RetroLoom/LPT2FDD/Images/LPT2FDD_3D.png

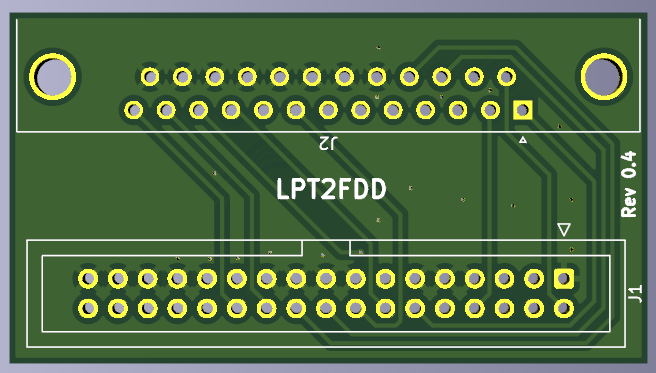
Images/LPT2FDD_3D.png
