RetroLoom/LPT2FDD/Power Adapter - PS2/4x1md/docs/images/3.5mm_6_contacts_4_conductors_audio_plug.png

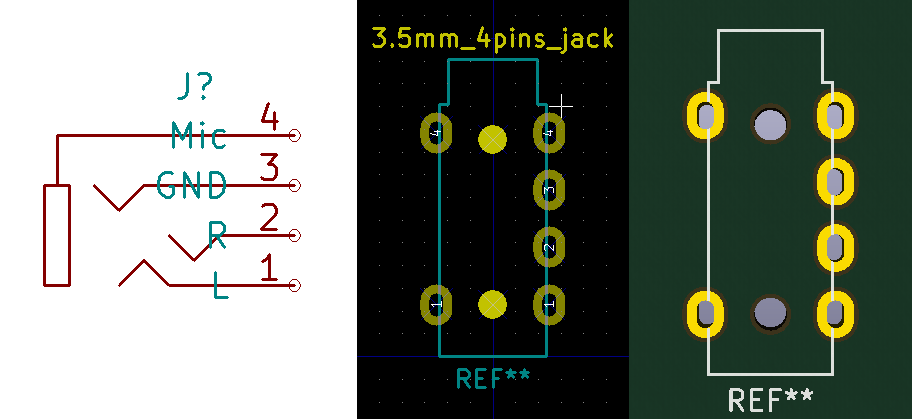
Power Adapter - PS2/4x1md/docs/images/3.5mm_6_contacts_4_conductors_audio_plug.png
