RetroLoom/LPT2FDD/Power Adapter - PS2/4x1md/docs/images/Connector_MiniDIN_Female_6Pin_2rows_footprints.png

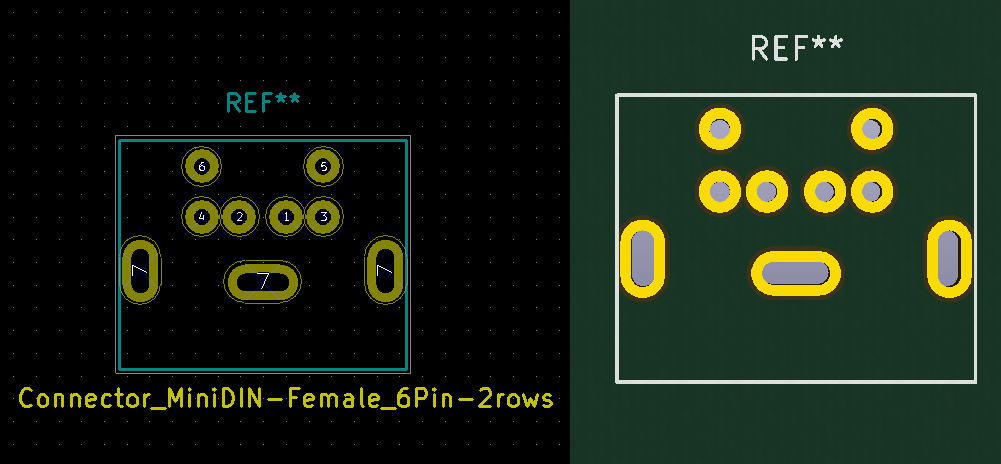
Power Adapter - PS2/4x1md/docs/images/Connector_MiniDIN_Female_6Pin_2rows_footprints.png
