RetroLoom/LPT2FDD/Power Adapter - PS2/4x1md/docs/images/datasheets/Cliff_UT1x.png

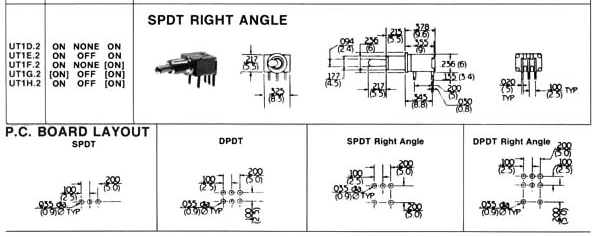
Power Adapter - PS2/4x1md/docs/images/datasheets/Cliff_UT1x.png
