RetroLoom/LPT2FDD/Power Adapter - PS2/4x1md/docs/images/datasheets/Connector_MiniDIN_Female_6Pin_2rows.png

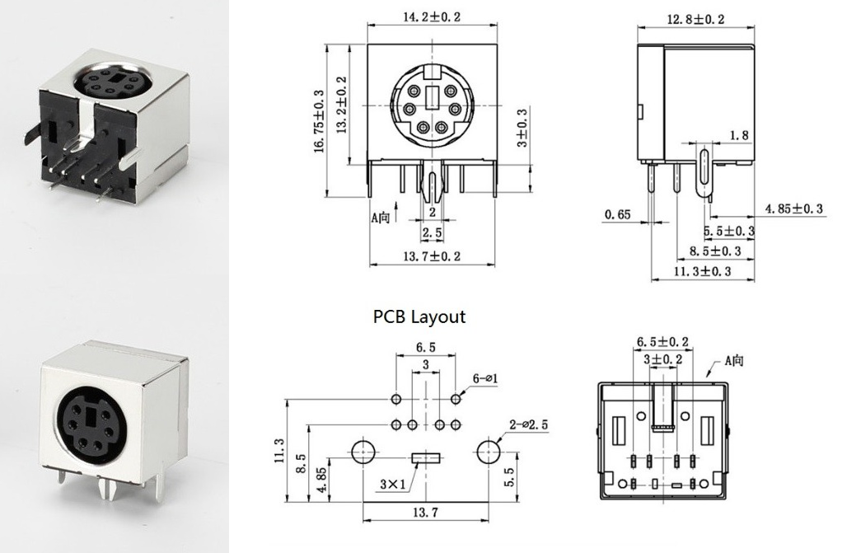
Power Adapter - PS2/4x1md/docs/images/datasheets/Connector_MiniDIN_Female_6Pin_2rows.png
