RetroLoom/LPT2FDD/Power Adapter - PS2/4x1md/docs/images/datasheets/Gms-g9_GNSS_Module.png

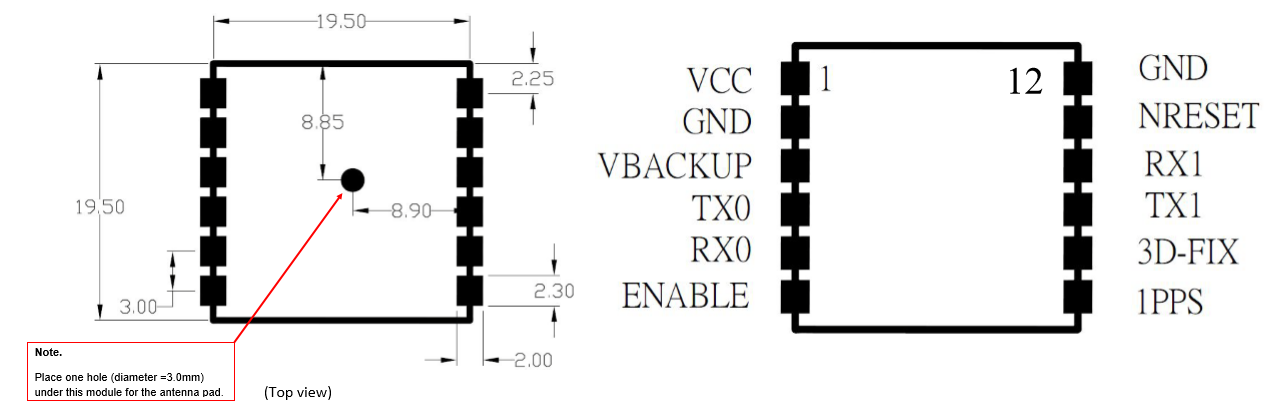
Power Adapter - PS2/4x1md/docs/images/datasheets/Gms-g9_GNSS_Module.png
