RetroLoom/LPT2FDD/Power Adapter - PS2/4x1md/docs/images/datasheets/Jack PJ-311D.jpg

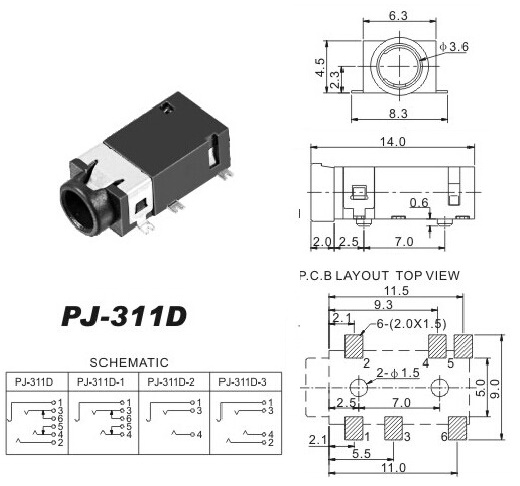
Power Adapter - PS2/4x1md/docs/images/datasheets/Jack PJ-311D.jpg
