RetroLoom/LPT2FDD/Power Adapter - PS2/4x1md/docs/images/datasheets/Philmore_30-20001_SPDT_Switch.png

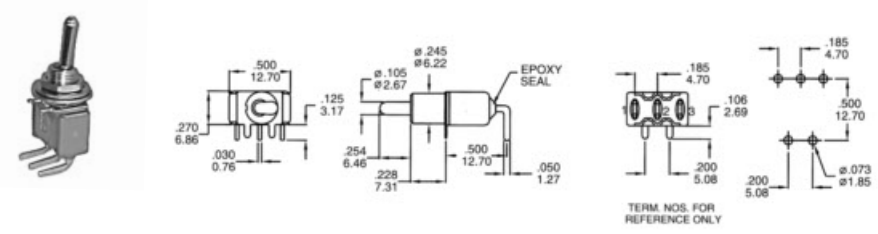
Power Adapter - PS2/4x1md/docs/images/datasheets/Philmore_30-20001_SPDT_Switch.png
