RetroLoom/LPT2FDD/Power Adapter - PS2/4x1md/docs/images/datasheets/PJ-320DS.png

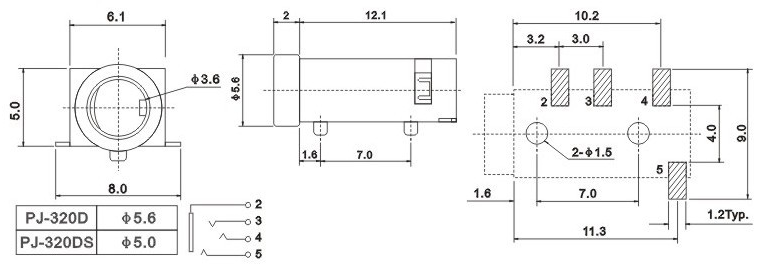
Power Adapter - PS2/4x1md/docs/images/datasheets/PJ-320DS.png
