RetroLoom/LPT2FDD/Power Adapter - PS2/4x1md/docs/images/datasheets/Quectel_L80_GPS_Module_2.png

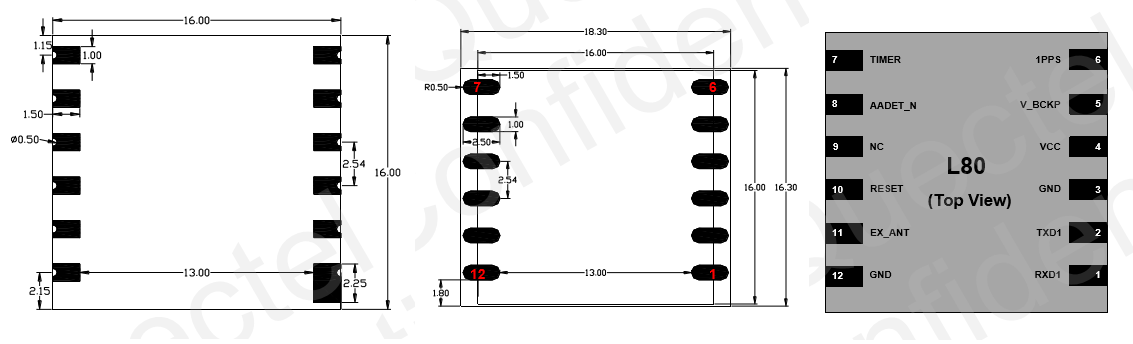
Power Adapter - PS2/4x1md/docs/images/datasheets/Quectel_L80_GPS_Module_2.png
