RetroLoom/LPT2FDD/Power Adapter - PS2/4x1md/docs/images/datasheets/Seiko_MS621FE-FL11E_dia.png

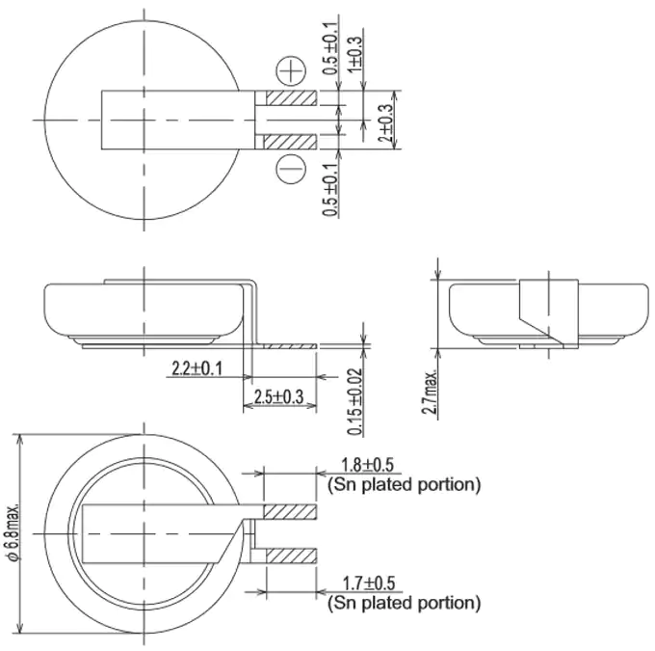
Power Adapter - PS2/4x1md/docs/images/datasheets/Seiko_MS621FE-FL11E_dia.png
