RetroLoom/LPT2FDD/Power Adapter - PS2/4x1md/docs/images/datasheets/USB Micro 5 pin SMT B.jpg

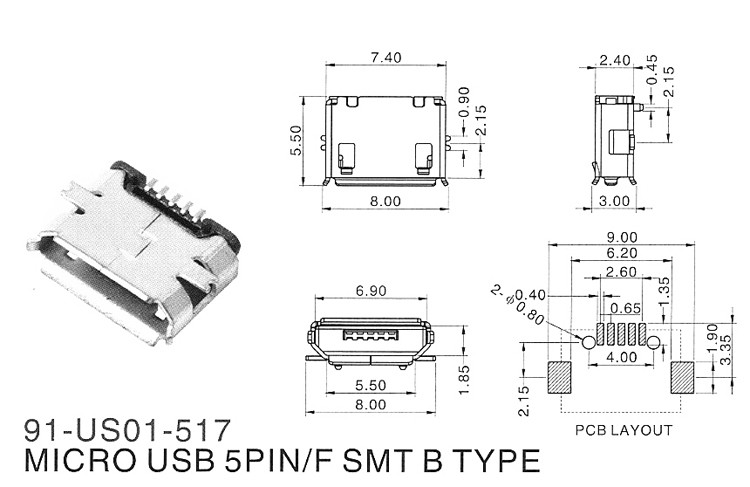
Power Adapter - PS2/4x1md/docs/images/datasheets/USB Micro 5 pin SMT B.jpg
