RetroLoom/LPT2FDD/Power Adapter - PS2/4x1md/docs/images/datasheets/USB Micro 5pin Through hole.jpg

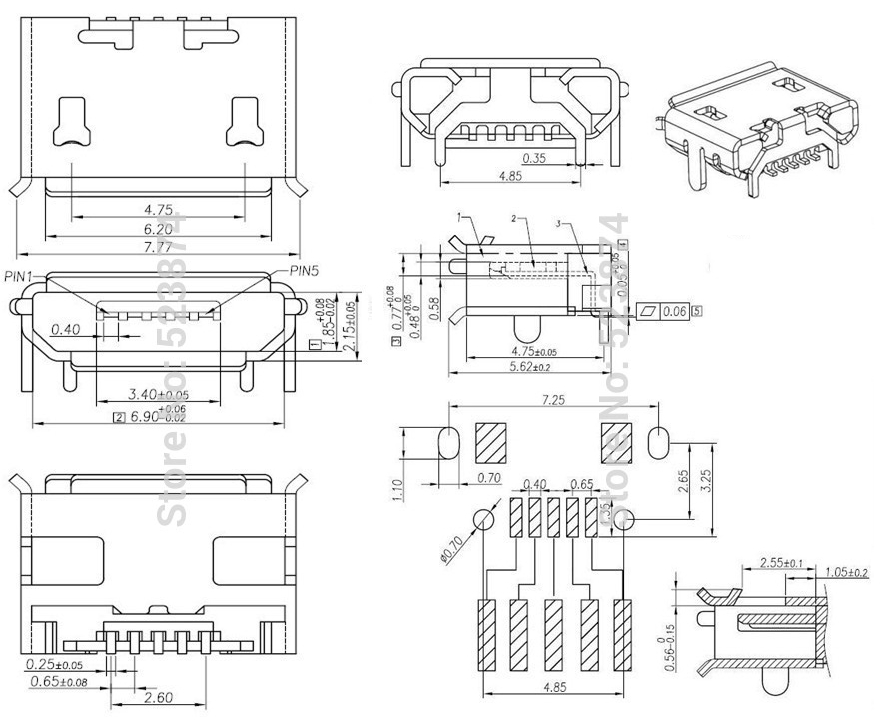
Power Adapter - PS2/4x1md/docs/images/datasheets/USB Micro 5pin Through hole.jpg
