RetroLoom/LPT2FDD/Power Adapter - PS2/4x1md/docs/images/datasheets/USB_Mini_Vertical.jpg

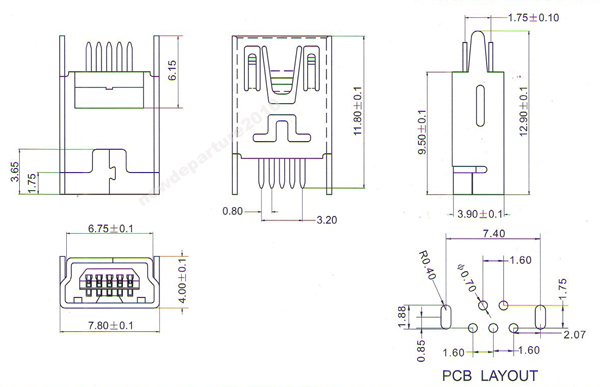
Power Adapter - PS2/4x1md/docs/images/datasheets/USB_Mini_Vertical.jpg
