RetroLoom/LPT2FDD/Power Adapter - PS2/4x1md/docs/images/footprints_01.png

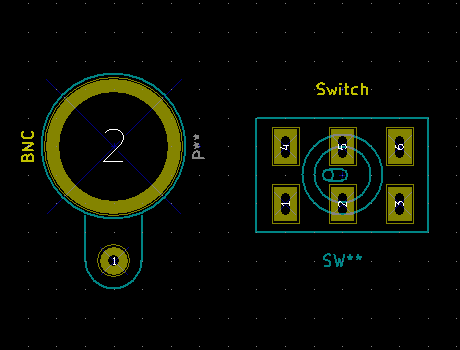
Power Adapter - PS2/4x1md/docs/images/footprints_01.png
