RetroLoom/LPT2FDD/Power Adapter - PS2/4x1md/docs/images/microampermeter.jpg

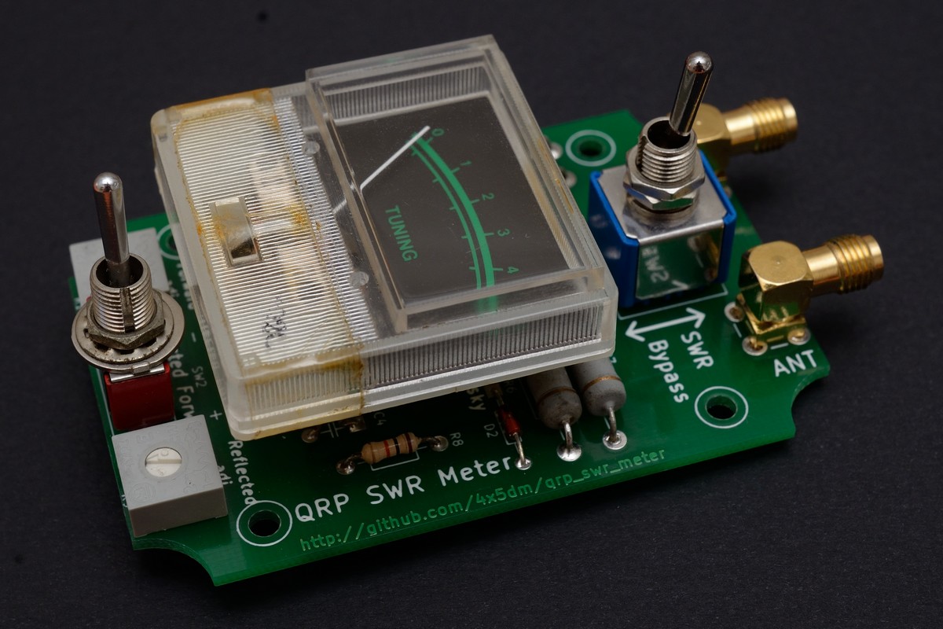
Power Adapter - PS2/4x1md/docs/images/microampermeter.jpg
