RetroLoom/LPT2FDD/Power Adapter - PS2/4x1md/docs/images/microampermeter.png

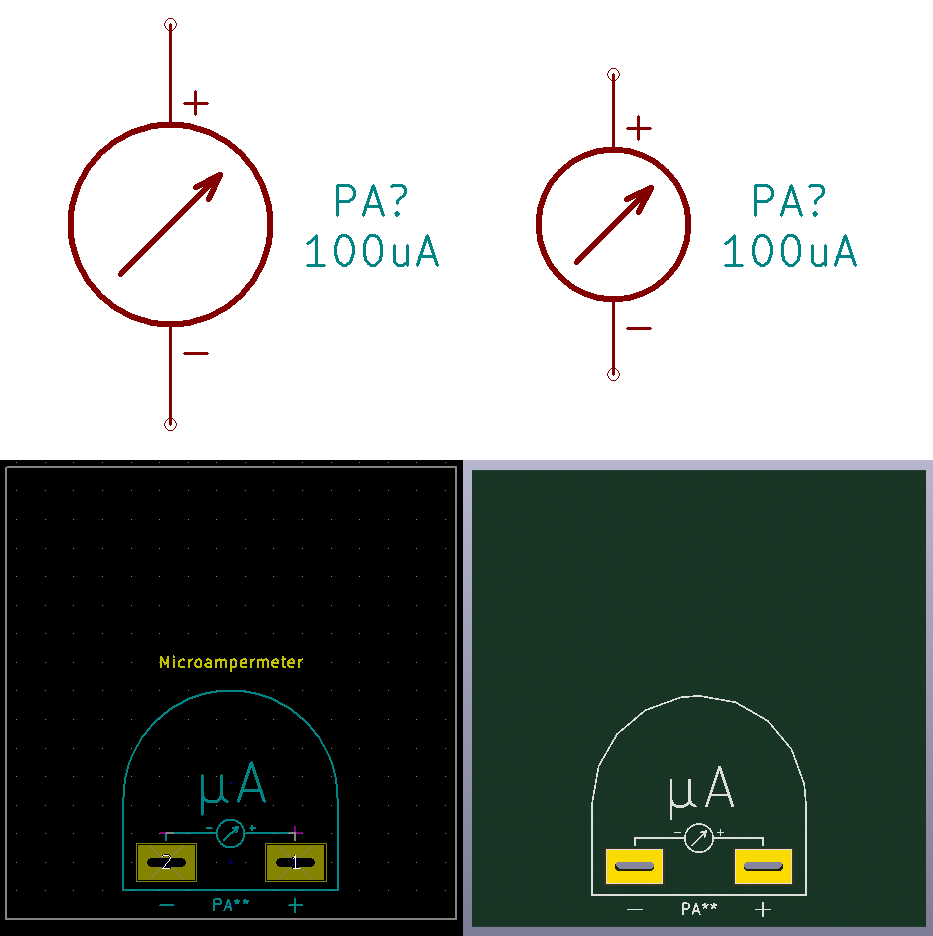
Power Adapter - PS2/4x1md/docs/images/microampermeter.png
