RetroLoom/LPT2FDD/Power Adapter - PS2/4x1md/docs/images/mini_usb_throughhole.png

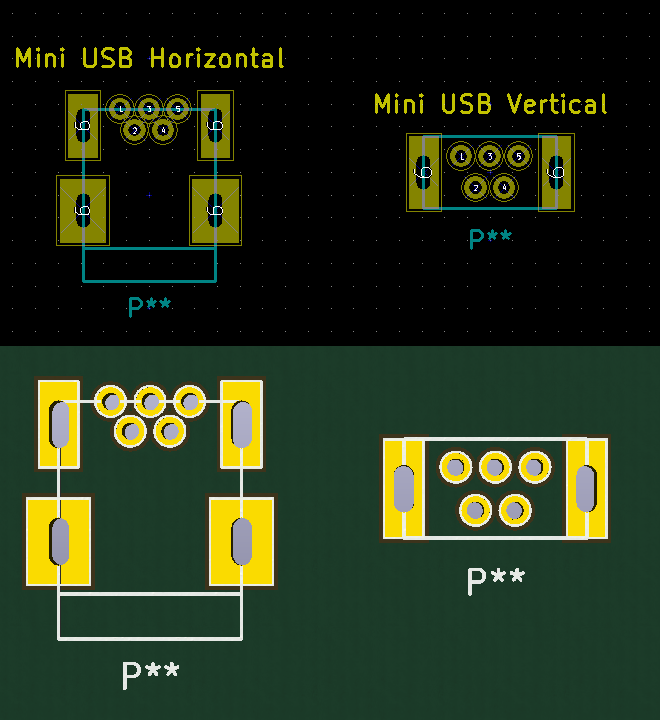
Power Adapter - PS2/4x1md/docs/images/mini_usb_throughhole.png
