RetroLoom/LPT2FDD/Power Adapter - PS2/4x1md/docs/images/PJ-311D.png

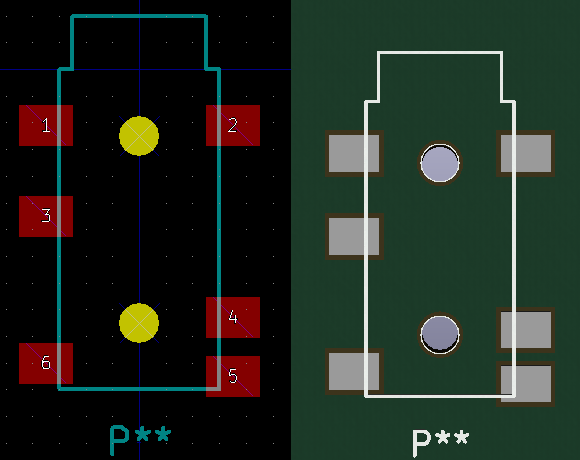
Power Adapter - PS2/4x1md/docs/images/PJ-311D.png
