RetroLoom/LPT2FDD/Power Adapter - PS2/4x1md/docs/images/PJ-320D_footprint.png

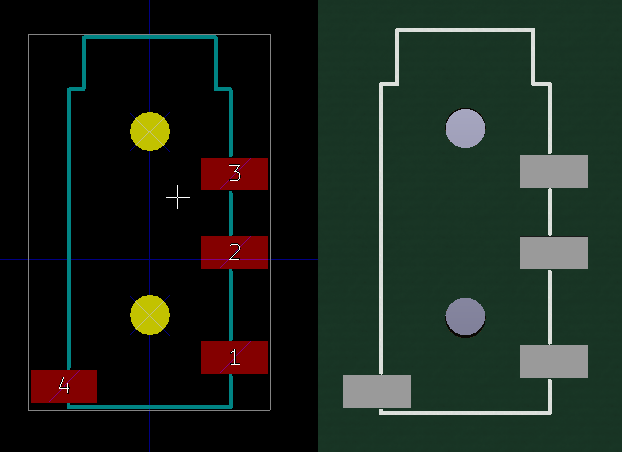
Power Adapter - PS2/4x1md/docs/images/PJ-320D_footprint.png
