RetroLoom/LPT2FDD/Power Adapter - PS2/4x1md/docs/images/PJ-320DS.jpg

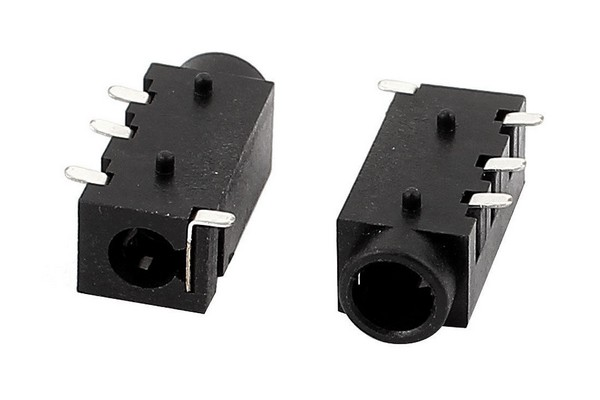
Power Adapter - PS2/4x1md/docs/images/PJ-320DS.jpg
