RetroLoom/LPT2FDD/Power Adapter - PS2/4x1md/docs/images/PJ-320E_footprint.png

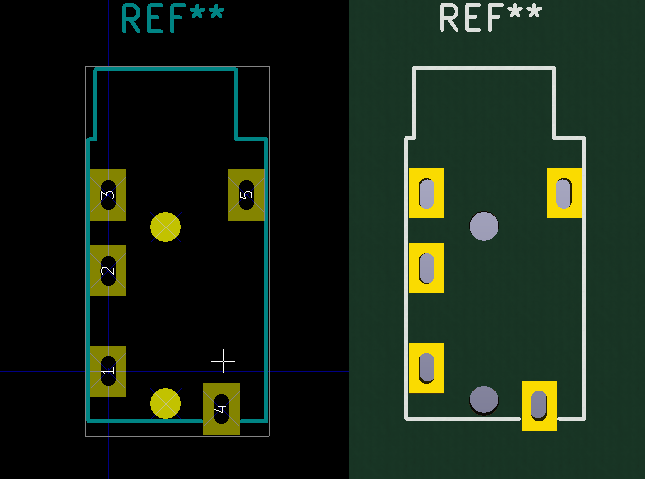
Power Adapter - PS2/4x1md/docs/images/PJ-320E_footprint.png
