RetroLoom/LPT2FDD/Power Adapter - PS2/4x1md/docs/images/PJ-31060.png

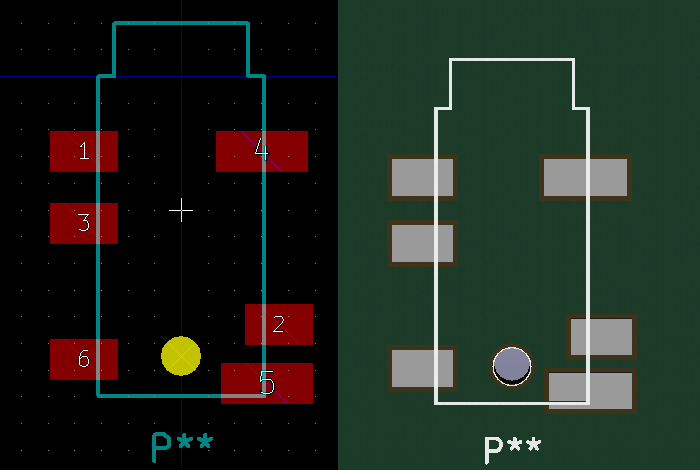
Power Adapter - PS2/4x1md/docs/images/PJ-31060.png
