RetroLoom/LPT2FDD/Power Adapter - PS2/4x1md/docs/images/Quectel_L80_GPS_Module.jpg

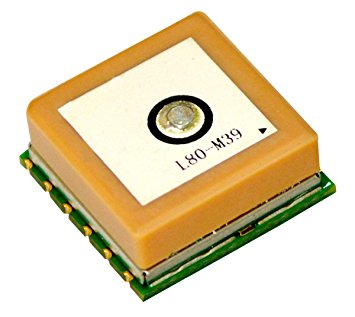
Power Adapter - PS2/4x1md/docs/images/Quectel_L80_GPS_Module.jpg
