RetroLoom/LPT2FDD/Power Adapter - PS2/4x1md/docs/images/SPDT-slide-switch.png

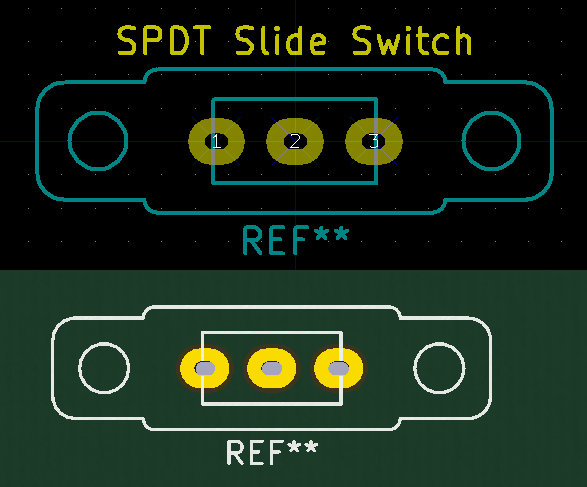
Power Adapter - PS2/4x1md/docs/images/SPDT-slide-switch.png
