RetroLoom/LPT2FDD/Power Adapter - PS2/4x1md/docs/images/symbols_01.png

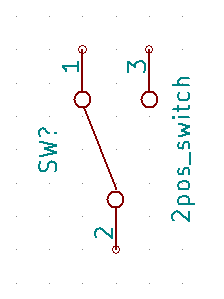
Power Adapter - PS2/4x1md/docs/images/symbols_01.png
