RetroLoom/LPT2FDD/Power Adapter - PS2/4x1md/docs/images/installation/footprints_4.png

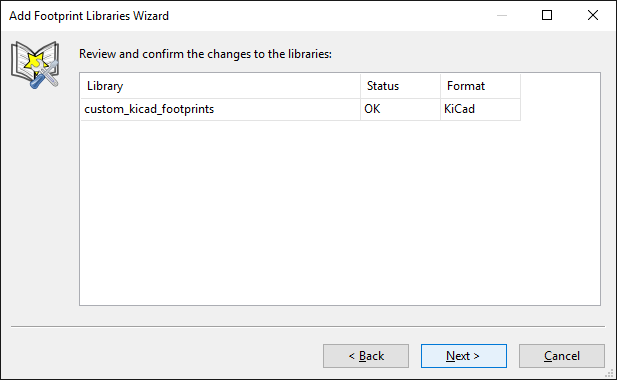
Power Adapter - PS2/4x1md/docs/images/installation/footprints_4.png
