RetroLoom/LPT2FDD/Power Adapter - PS2/4x1md/docs/images/installation/symbols_1.png

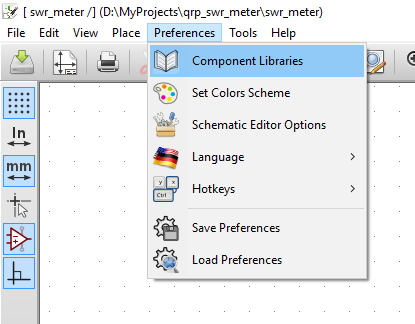
Power Adapter - PS2/4x1md/docs/images/installation/symbols_1.png
